undefined-rainy-storm/embedded-rhythm-game-controller/controller/global.h

#include "keymap.h"
#include "flags.h"

#ifndef GLOBAL
#define GLOBAL

class Global {
private:
  Global();

  Global(const Global&) = delete;
  Global& operator=(const Global&) = delete;

  keymap_t _keymap;
public:
  static Global *getInstance();
  void putEEPROM();
  void getEEPROM();

  KeymapConfig keymap;
  SerialCommState serialCommState;  
};

#endif
