undefined-rainy-storm/embedded-rhythm-game-controller/controller/magic.h

#ifndef MAGIC
#define MAGIC

#define MAGIC_LENGTH 9
#define KEYMAP_LENGTH 28
#define HANDSHAKE_REQUEST         { 0x2e, 0x68, 0x73, 0x2e, 0x74, 0x72, 0x79, 0x2e, 0x68 }
#define HANDSHAKE_RESPONSE        { 0x2e, 0x68, 0x73, 0x2e, 0x72, 0x65, 0x73, 0x2e, 0x61 }
#define LOAD_KEY_CONFIG_REQUEST   { 0x2e, 0x6b, 0x63, 0x2e, 0x72, 0x65, 0x71, 0x2e, 0x68 }
#define LOAD_KEY_CONFIG_RESPONSE  { 0x2e, 0x6b, 0x63, 0x2e, 0x72, 0x65, 0x73, 0x2e, 0x61 }
#define SET_KEY_CONFIG_REQUEST    { 0x2e, 0x73, 0x63, 0x2e, 0x72, 0x65, 0x71, 0x2e, 0x68 }
#define SET_KEY_CONFIG_REQUEST_INCOMPLETE \
                                  { 0x2e, 0x73, 0x63, 0x2e, 0x72, 0x65, 0x73, 0x2e, 0x62 }
#define SET_KEY_CONFIG_RESPONSE   { 0x2e, 0x73, 0x63, 0x2e, 0x72, 0x65, 0x73, 0x2e, 0x61 }

#endif
