undefined-rainy-storm/embedded-rhythm-game-controller/controller/keyboard_handler.h

#include <Keyboard.h>
#include "pin.h"
#include "default.h"

#ifndef KEYBOARD_HANDLER
#define KEYBOARD_HANDLER

void onSetup_beginPinModeAsInputPullup();
void onLoop_handlePullupButtonState();

#endif
