undefined-rainy-storm/embedded-rhythm-game-controller/controller/button.h

#ifndef BUTTON
#define BUTTON

enum button {
  esc, enter, tab, space,
  speed_up, speed_down, rewind_key,
  left_shift, right_shift,
  arrow_up, arrow_down, arrow_left, arrow_right,
  tune_left_side, tune_s, tune_d, tune_f, tune_c, tune_m, tune_j, tune_k, tune_l, tune_right_side,
  emoticon1, emoticon2, emoticon3, emoticon4, emoticon5
} typedef Button;
#endif
